KaiPereira/PR1SM/renders/render.png

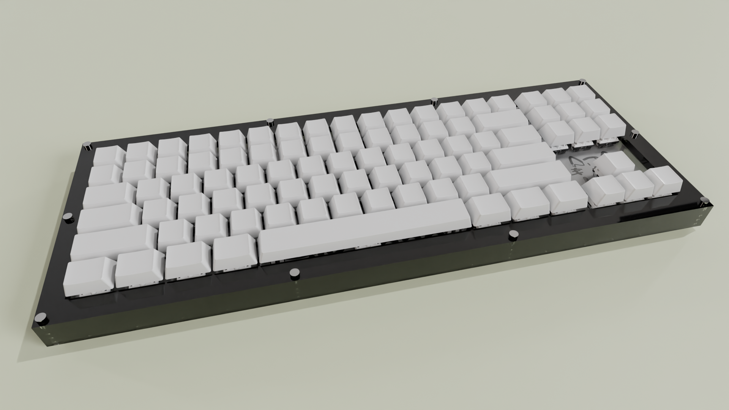
renders/render.png
