KaiPereira/PR1SM/journal/IMG_1544.jpg

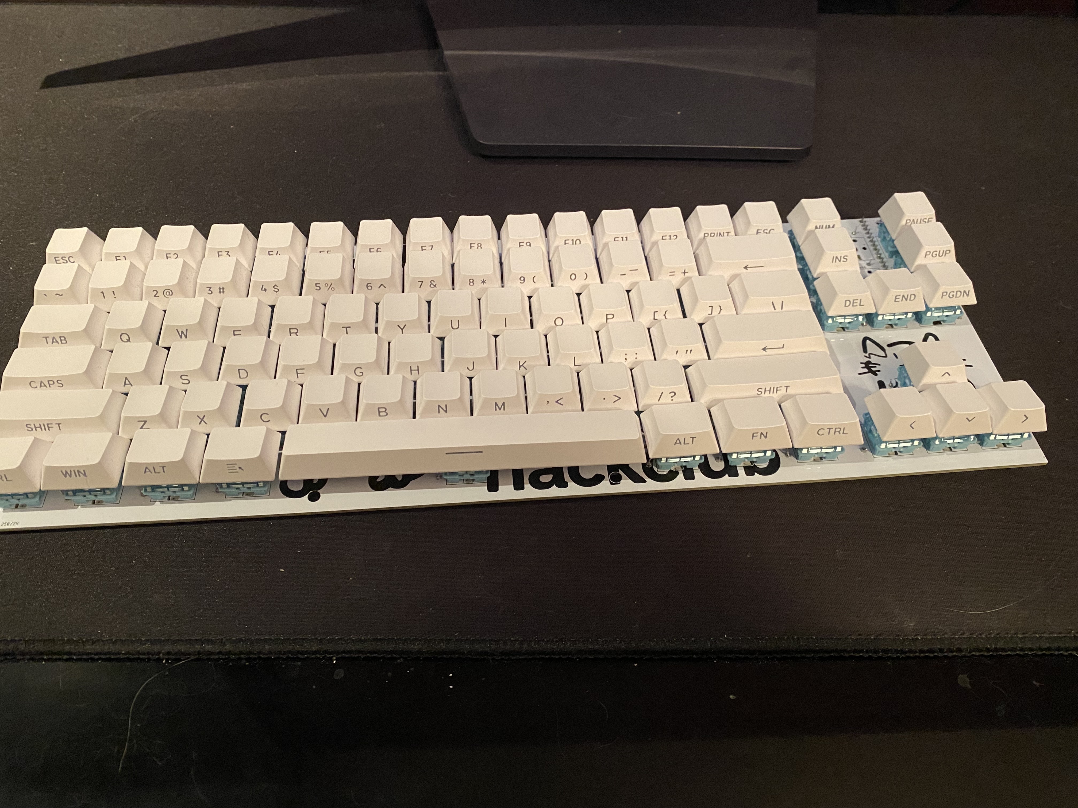
journal/IMG_1544.jpg
