KaiPereira/PR1SM/journal/Pasted image 20250718024216.png

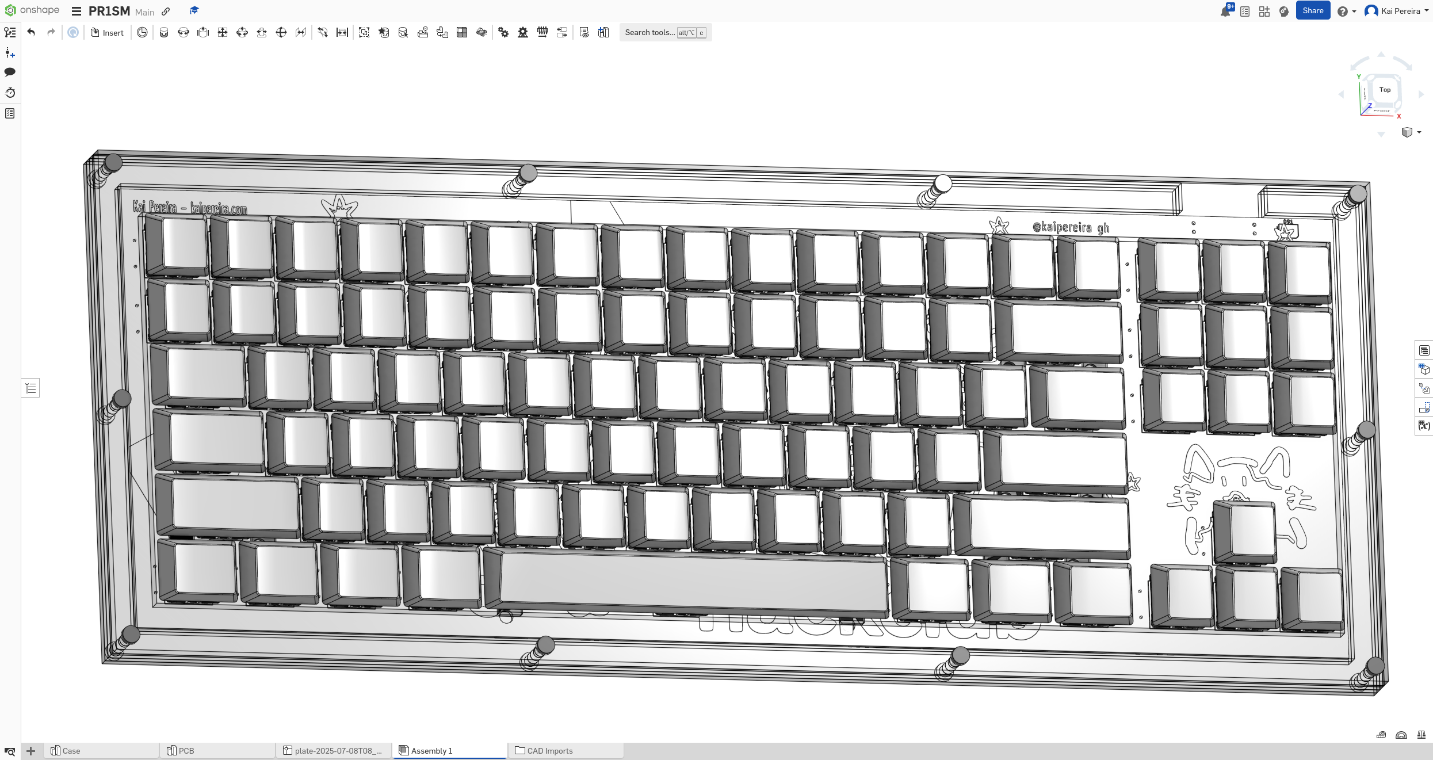
journal/Pasted image 20250718024216.png
